MrCodingRobot/EmergencyStations/Documentation/reports/trip_10_12_2019/image1.jpg

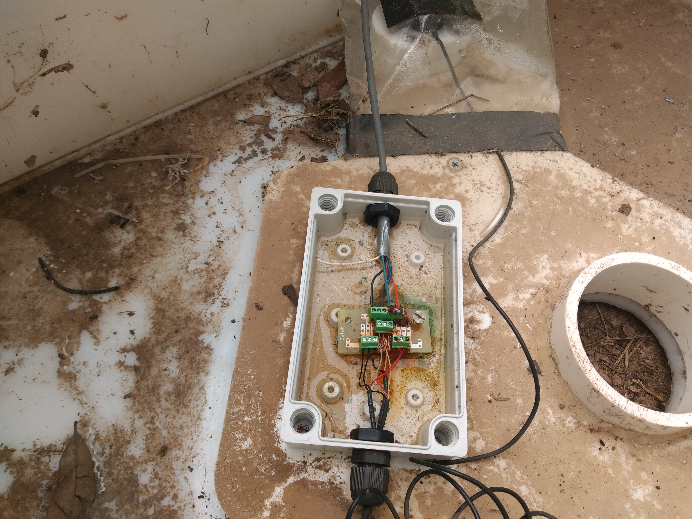
Documentation/reports/trip_10_12_2019/image1.jpg
