MrCodingRobot/EmergencyStations/Documentation/reports/trip_10_12_2019/image2.jpg

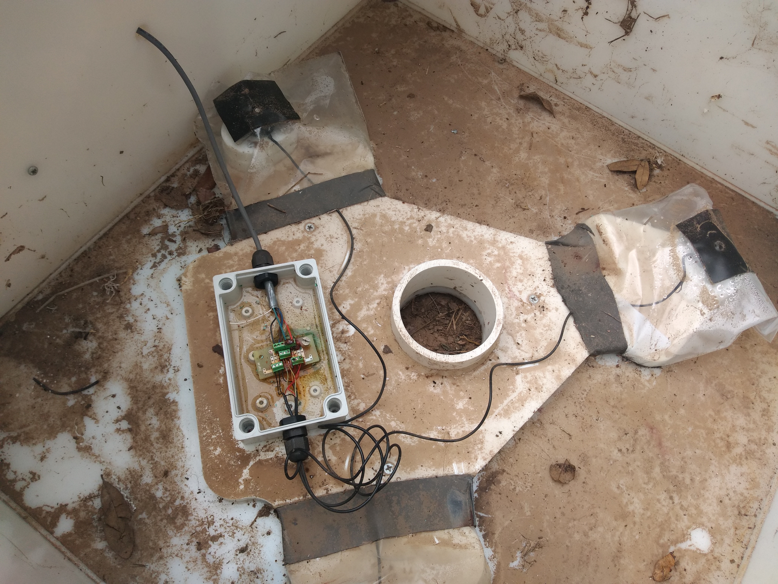
Documentation/reports/trip_10_12_2019/image2.jpg
