MrCodingRobot/EmergencyStations/Software/NetworkControl/generated_data/Station1.png

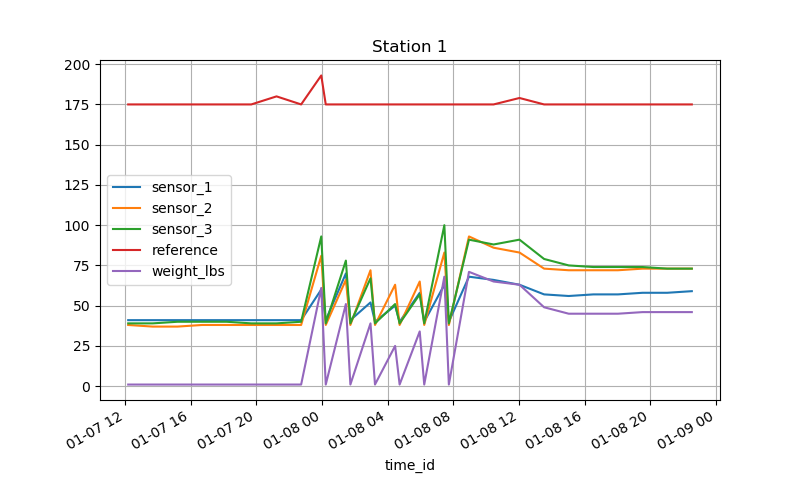
Software/NetworkControl/generated_data/Station1.png
