MrCodingRobot/EmergencyStations/Software/NetworkControl/generated_data/Station2.png

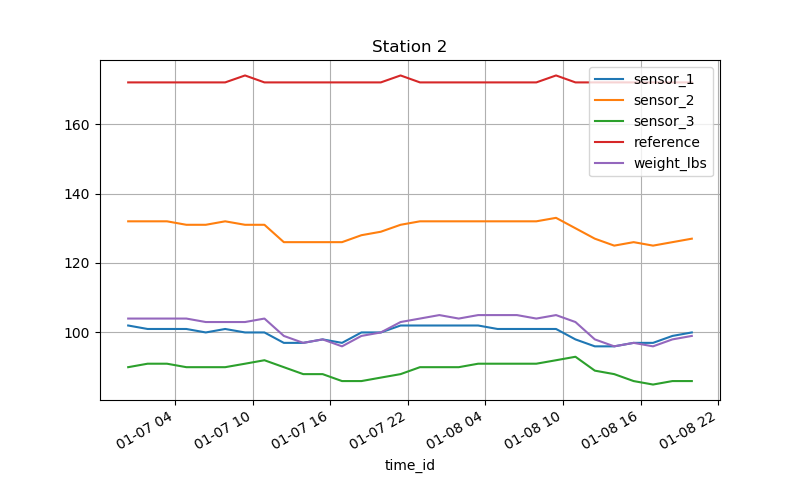
Software/NetworkControl/generated_data/Station2.png
