MrCodingRobot/EmergencyStations/Software/NetworkControl/generated_data/Station3.png

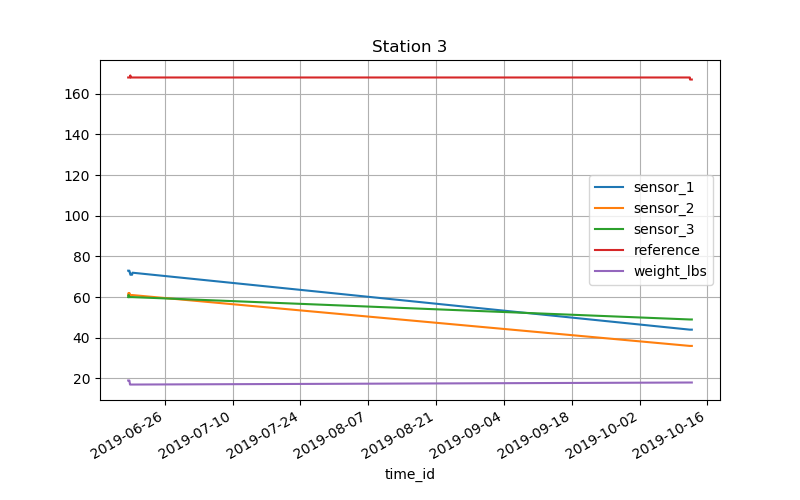
Software/NetworkControl/generated_data/Station3.png
