MrCodingRobot/EmergencyStations/Software/NetworkControl/generated_data/Station4.png

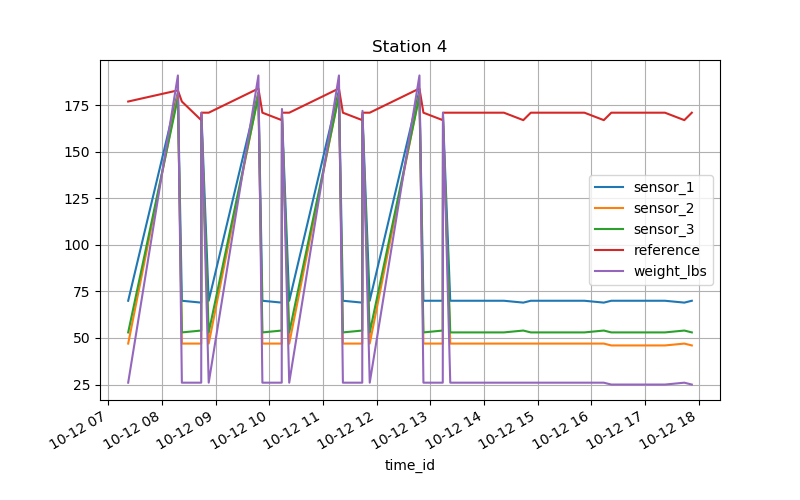
Software/NetworkControl/generated_data/Station4.png
