MrCodingRobot/EmergencyStations/Software/NetworkControl/generated_data/Station5.png

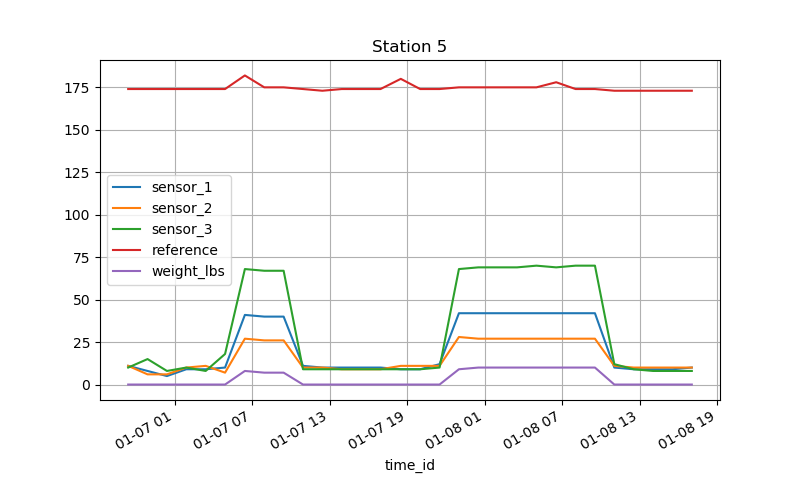
Software/NetworkControl/generated_data/Station5.png
