MrCodingRobot/EmergencyStations/Documentation/reports/maintenance_1_26_2020/stations_historical_data/water_level_charts-4-1.jpg

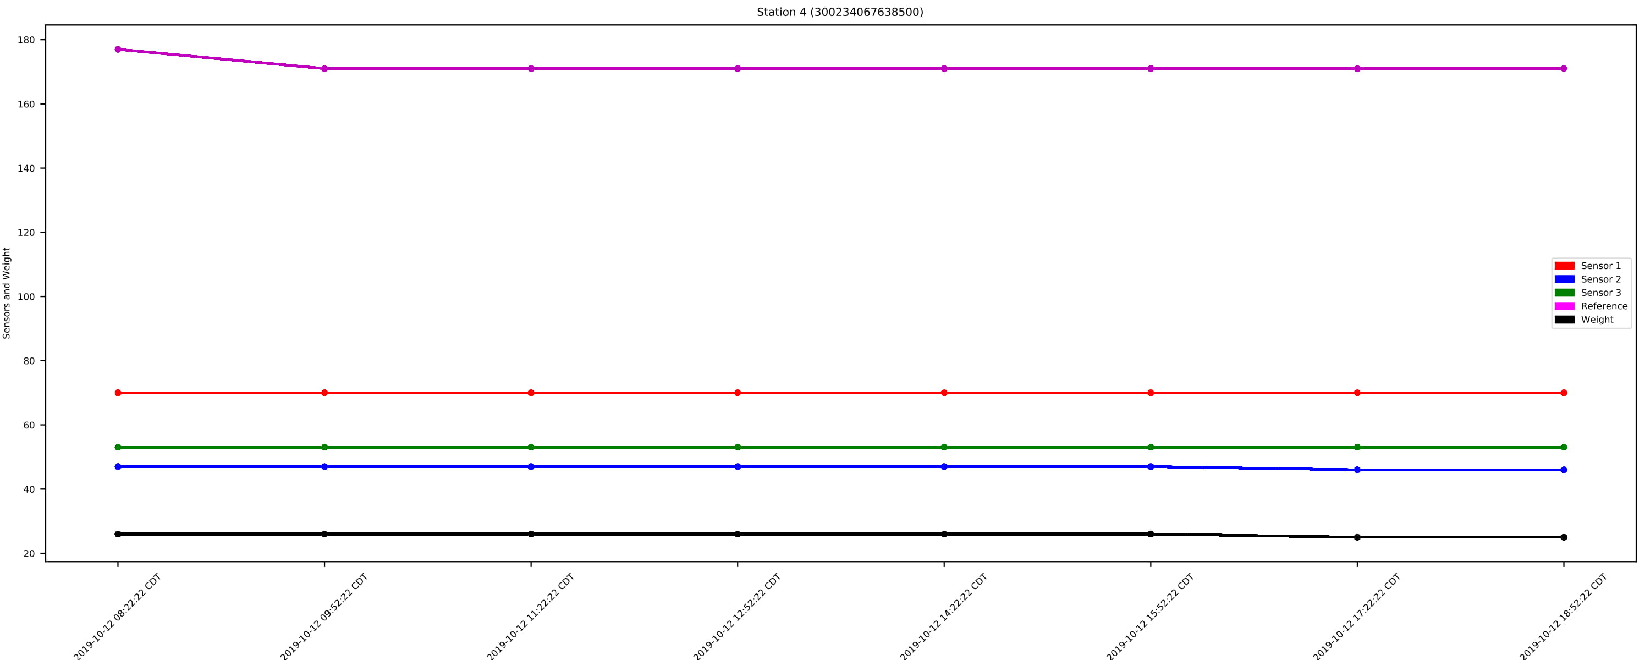
Documentation/reports/maintenance_1_26_2020/stations_historical_data/water_level_charts-4-1.jpg
