MrCodingRobot/EmergencyStations/Software/NetworkControl/misc/problem.png

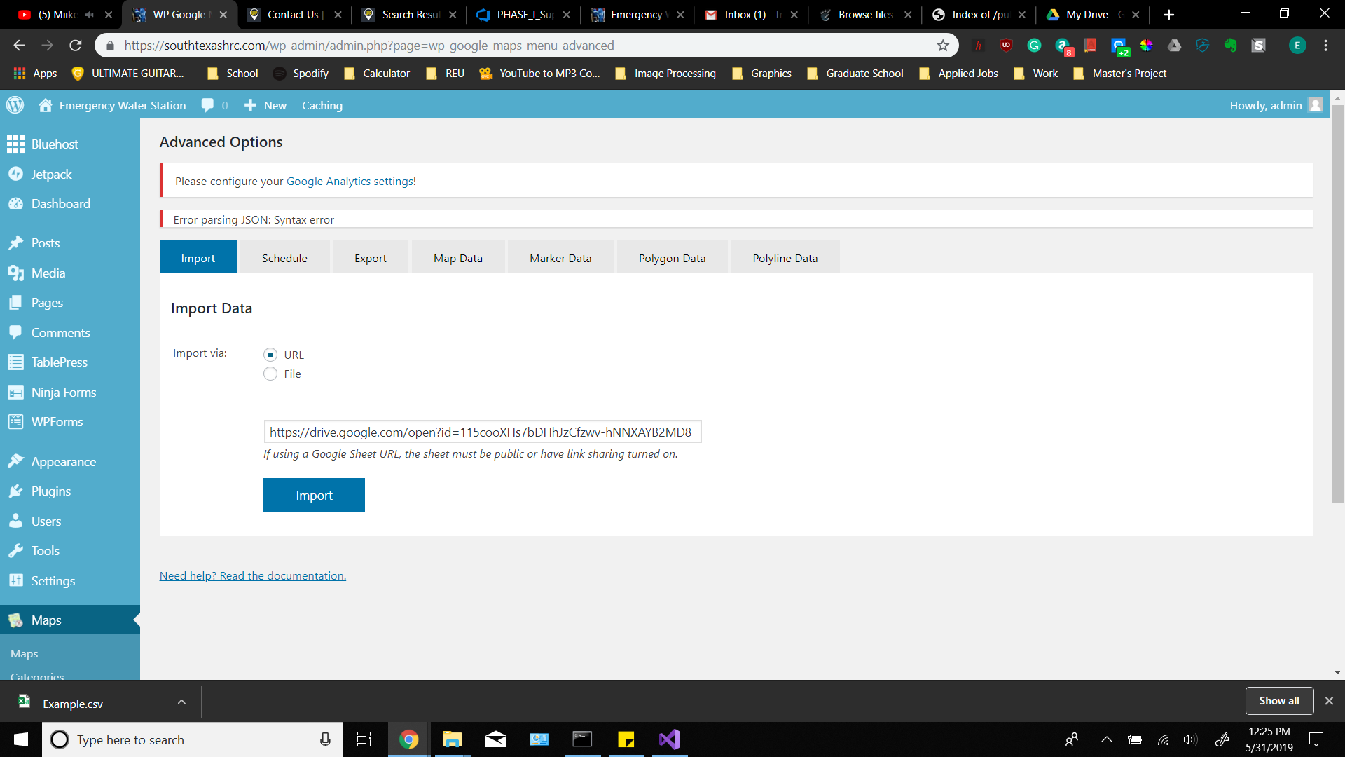
Software/NetworkControl/misc/problem.png
