MrCodingRobot/EmergencyStations/Software/Arduino/Phase1_V4/DataCollection.ino

// Serial Handling

void serialFlush(){

  /*
  This function clears all the entered character's in the
  Serial buffer. This function is used to allow the
  while(Serial.avaliable() == 0){} to effectively wait
  for the user's command.
  */

  while(Serial.available() > 0){
    char t = Serial.read();
  }
}

void serialObtainNumber(){

  /*
  This function obtains the value of the given weight value from
  Serial.
  */

  while(Serial.available() == 0){}
  placed_test_weight = Serial.parseFloat();

  Serial.print("PLACED TEST WEIGHT VALUE: ");
  Serial.print(placed_test_weight, 5);
  Serial.println(" (lbs)");

}

void printDataArray(){

  /*
  This function just provides the necessary format to printout
  all the data contained within the data array.
  */

  Serial.println();
  Serial.println("@@@@@@@@@@@@@@@@@@@@@@@@@@@@@@@@@@@@");
  Serial.println("Printing Complete Array Values");

  // Station Information
  Serial.print("[0]: Station Number: ");
  Serial.println(data_pointer[0]);

  // Alarm Values
  Serial.print("[1]: Alarms: ");
  Serial.println(data_pointer[1]);

  int set_counter = 1;
  for (int index = 2; index < DATA_ARRAY_SIZE - (2 + 5); index += 5){

    // Set Index Printing
    Serial.println();
    Serial.print("******** ");
    Serial.print("(");
    Serial.print(set_counter);
    Serial.print(" / 8)");
    Serial.println(" ********");

    // Value Printing
    Serial.print("[");
    Serial.print(index);
    Serial.print("]: Sensor 1: ");
    Serial.println(data_pointer[index]);

    Serial.print("[");
    Serial.print(index + 1);
    Serial.print("]: Sensor 2: ");
    Serial.println(data_pointer[index + 1]);

    Serial.print("[");
    Serial.print(index + 2);
    Serial.print("]: Sensor 3: ");
    Serial.println(data_pointer[index + 2]);

    Serial.print("[");
    Serial.print(index + 3);
    Serial.print("]: Reference: ");
    Serial.println(data_pointer[index + 3]);

    Serial.print("[");
    Serial.print(index + 4);
    Serial.print("]: Weight: ");
    Serial.println(data_pointer[index + 4]);

    set_counter++;
  }

  Serial.println("@@@@@@@@@@@@@@@@@@@@@@@@@@@@@@@@@@@@");
}

//////////////////////////////////////////////////////////
// Calibration Routines

void zeroWeightCalibration(){

  /*
  This function collects the values of the sensor's output
  without any additional weight placed above the sensors. This
  helps us only calculate the weight actually placed above these
  values.
  */

  Serial.println("ZERO WEIGHT MEASUREMENT: PRESS ANY KEY TO TRIGGER");
  while(Serial.available() == 0){}
  serialFlush();
  Serial.println("ZERO WEIGHT MEASUREMENT: PERFORMING MEASUREMENT");

  // Obtaining the value of the weight sensors
  for (uint32_t i = 0; i < (sizeof(zero_weight_sensor_values) / sizeof(zero_weight_sensor_values[0])); i++){

    for (uint32_t j = 0; j < NUMBER_OF_SAMPLES; j++){
      zero_weight_sensor_values[i] += analogRead(WEIGHT_SENSORS_PINS[i]);
    }

    zero_weight_sensor_values[i] = zero_weight_sensor_values[i]/NUMBER_OF_SAMPLES; // Averaging Value
  }

  // Report of Zero Weight Measurement
  for (uint32_t i = 0; i < (sizeof(zero_weight_sensor_values) / sizeof(zero_weight_sensor_values[0])); i++){
    Serial.print("Sensor ");
    Serial.print(i);
    Serial.print(": ");
    Serial.println(zero_weight_sensor_values[i]);
  }
}

void barrelWeightCalibration(){

  /*
  This function handles with the weighing of the barrel placed on top of
  the weight sensors. While still using a hard-coded value for the sensor's
  voltage output and lbs slope/ratio, the barrel weight calibration needs
  to happen before because the barrel provides the necessary platform to properly
  calculate the slope/ratio.
  */

  Serial.println("BARREL WEIGHT MEASUREMENT: PRESS ANY KEY TO TRIGGER");
  while(Serial.available() == 0){}
  serialFlush();
  Serial.println("BARREL WEIGHT MEASUREMENT: PERFORMING MEASUREMENT");

  // Obtaining the value of the weight sensors
  for (uint32_t i = 0; i < (sizeof(barrel_weight_sensor_values) / sizeof(barrel_weight_sensor_values[0])); i++){

    for (uint32_t j = 0; j < NUMBER_OF_SAMPLES; j++){
      barrel_weight_sensor_values[i] += analogRead(WEIGHT_SENSORS_PINS[i]);
    }

    barrel_weight_sensor_values[i] = barrel_weight_sensor_values[i]/NUMBER_OF_SAMPLES; // Averaging Value
    barrel_weight_sensor_value += barrel_weight_sensor_values[i] - zero_weight_sensor_values[i];
  }

  // Report of Zero Weight Measurement
  for (uint32_t i = 0; i < (sizeof(barrel_weight_sensor_values) / sizeof(barrel_weight_sensor_values[0])); i++){
    Serial.print("Sensor ");
    Serial.print(i);
    Serial.print(": ");
    Serial.println(barrel_weight_sensor_values[i]);
  }

  barrel_weight = barrel_weight_sensor_value * ADC2LBS_SLOPE;
  Serial.print("Barrel Weight (with pre-set adc2lbs_slope value): ");
  Serial.println(barrel_weight);
}

void slopeCalibration(){

  /*
  This function handles the calibration of the slope between the sensor's value
  and the actual lbs placed on top of the sensor. This slope can also be considered
  as the ratio between sensor's voltage output and physical lbs of weight.
  */

  Serial.println("ADC2LBS_SLOPE MEASUREMENT: PRESS ANY KEY TO TRIGGER");
  while(Serial.available() == 0){}
  serialFlush();
  Serial.println("ADC2LBS_SLOPE MEASUREMENT: PERFORMING MEASUREMENT");

  Serial.println("ENTER PLACED TEST WEIGHT (LBS):");
  serialObtainNumber();
  serialFlush();

  // Obtaning the value of the weight sensors
  for (uint32_t i = 0; i < (sizeof(slope_weight_sensor_values) / sizeof(slope_weight_sensor_values[0])); i++){

    for (uint32_t j = 0; j < NUMBER_OF_SAMPLES; j++){
      slope_weight_sensor_values[i] += analogRead(WEIGHT_SENSORS_PINS[i]);
    }

    slope_weight_sensor_values[i] = slope_weight_sensor_values[i]/NUMBER_OF_SAMPLES; // Averaging Value
    slope_weight_sensor_value += slope_weight_sensor_values[i] - (barrel_weight_sensor_values[i]);
  }

  // Calculating the slope value
  Serial.print("Slope weight sensor value: ");
  Serial.println(slope_weight_sensor_value);

  adc2lbs_slope = placed_test_weight / slope_weight_sensor_value;

  // Report of ADC2LBS Slope Calibration
  Serial.print("ADC2LBS_SLOPE: ");
  Serial.println(adc2lbs_slope, 5);

  // Report of Barrel Weight with new ADC2LBS Slope value
  barrel_weight = barrel_weight_sensor_value * adc2lbs_slope;
  Serial.print("Barrel Weight (with calculated adc2lbs_slope value): ");
  Serial.println(barrel_weight);

}

void calibrationRoutine(){

  /*
  This function does the calibration routine, which collected the sensor
  values for Zero Weight and the Barrel Weight. These two sets of data is
  later used in the dataCollection functions to calculate the additional
  weight placed after the barrel.
  */

  Serial.println("WEIGHT SENSOR CALIBRATION");

  // ***********************
  // Zero Weight Calibration
  // ***********************

  zeroWeightCalibration();

  // *************************
  // Barrel Weight Calibration
  // *************************

  barrelWeightCalibration();

  // *************************
  // ADC2LBS Slope Calibration
  // *************************

  slopeCalibration();

}

void printRawData(){

  uint32_t sensor_values[] = {0, 0, 0, 0};

  // Obtaining the value of the weight sensors
  for (uint32_t i = 0; i < (sizeof(sensor_values) / sizeof(sensor_values[0])); i++){

    for (uint32_t j = 0; j < NUMBER_OF_SAMPLES; j++){
      sensor_values[i] += analogRead(WEIGHT_SENSORS_PINS[i]);
    }

    sensor_values[i] = sensor_values[i]/NUMBER_OF_SAMPLES; // Averaging Value
  }

  Serial.print("S1 - ");
  Serial.print(sensor_values[0]);
  Serial.print(": S2 - ");
  Serial.print(sensor_values[1]);
  Serial.print(": S3 - ");
  Serial.print(sensor_values[2]);
  Serial.print(": S4 - ");
  Serial.println(sensor_values[3]);
  
}

//////////////////////////////////////////////////////////
// Single data collection and complete data collection

void dataCollection(int index){

  /*
  This function collects the data from the weight sensors, averages it according
  to the NUMBER_OF_SAMPLES variable, calculates the average weight of all sensors,
  and then calculates the weight of the jugs.
  */

  uint32_t sensor_values[] = {0, 0, 0, 0};

  // Obtaining the value of the weight sensors
  for (uint32_t i = 0; i < (sizeof(sensor_values) / sizeof(sensor_values[0])); i++){

    for (uint32_t j = 0; j < NUMBER_OF_SAMPLES; j++){
      sensor_values[i] += analogRead(WEIGHT_SENSORS_PINS[i]);
    }

    sensor_values[i] = sensor_values[i]/NUMBER_OF_SAMPLES; // Averaging Value
  }

  int accumulative_a2d_weight = 0;

  for (uint32_t k = 0; k < (sizeof(sensor_values) / sizeof(sensor_values[0])) - 1; k++){
    accumulative_a2d_weight += sensor_values[k] - barrel_weight_sensor_values[k];

  }

  // Calculating the weight from voltage to lbs (would prefer metric, but client wants imperial units >:S )
  //float weight_value = accumulative_a2d_weight * ADC2LBS_SLOPE;
  float weight_value = accumulative_a2d_weight * adc2lbs_slope;

  // Printing Values for Debugging
  Serial.println();
  Serial.print("&&&&&&&& ");
  Serial.print("(");
  Serial.print((index - 2) / 5 + 1);
  Serial.print(" / 8)");
  Serial.println(" &&&&&&&&");
  Serial.println("Raw Sensor Values");

  for (uint32_t i = 0; i < (sizeof(sensor_values) / sizeof(sensor_values[0])); i++){
    Serial.print("Sensor ");
    Serial.print(i);
    Serial.print(": ");
    Serial.println(sensor_values[i]);
  }

  Serial.print("Accumulative A2D Weight Value: ");
  Serial.println(accumulative_a2d_weight);

  Serial.print("Weight Value: ");
  Serial.println(weight_value, 3);

  // Setting alarms for the only last weight value
  if (index == 37){ // Latest Weight Value Only
    data[1] = ALL_GOOD;

    if (weight_value < (-0.5 * barrel_weight)){ // Barrel Removed
      data[1] = BARREL_REMOVED;
    }
    else if (weight_value < LOW_WEIGHT_TRIGGER){ // Low weight
      data[1] = LOW_WEIGHT;
    }
    else if (weight_value > 255){ // High Weight
      data[1] = HIGH_WEIGHT;
    }
  }

  // Safety capping and changing the variable type of weight_value
  uint32_t safe_weight_value = 0;
  if (weight_value > 255){
    safe_weight_value = 255;
  }
  else if (weight_value < 0){
    safe_weight_value = 0;
  }
  else{
    safe_weight_value = (uint32_t) weight_value;
  }

  // Rescaling values to fit within a byte
  for (int i = 0; i < (sizeof(sensor_values) / sizeof(sensor_values[0])); i++){
    sensor_values[i] = map(sensor_values[i], 0, 1023, 0, 255);
  }

  // Storing values into the data array
  data_pointer[index] = sensor_values[0]; // Sensor 1
  data_pointer[index + 1] = sensor_values[1]; // Sensor 2
  data_pointer[index + 2] = sensor_values[2]; // Sensor 3
  data_pointer[index + 3] = sensor_values[3]; // Reference Voltage
  data_pointer[index + 4] = safe_weight_value; // Weight Value, duh

  // For the last weight measurement, we place the value onto the
  // 45 index as well
  if (index == 37){
    data_pointer[45] = data_pointer[41];
  }

}

void completeDataCollection(float raw_delay_value, String delay_type){

  /*
  This function handles with the data collection over a period of time,
  with a delay in-between measurements of 'minute_delay' minute(s) apart.
  */
  int delay_multiplier = 1;

  if (delay_type == "seconds") delay_multiplier = 1;
  else if (delay_type == "minutes") delay_multiplier = 60;
  else if (delay_type == "hour") delay_multiplier = 60 * 60;
  else {
    // Defaulting to minutes
    delay_multiplier = 60;
    Serial.println("delay_type is invalid!");
  }

  long delay_value = round(1000 * raw_delay_value * delay_multiplier);

  for (int index = 2; index < DATA_ARRAY_SIZE - (2 + 5); index += 5){
    dataCollection(index);
    // 1000 millisecond => 1 second * 60 => 1 minute * minute_delay => minute_delay minutes
    delay(delay_value);
  }

  printDataArray();
}
